noeltaillardat/SmartGasSensor/ltspice/Draft1.asc

C1: cap; 100n
C2: cap; 1µ
C3: cap; 100n
C4: cap; 100n
I1: current; PULSE(50nA 100nA 2s 0.1s 0.1s 2s); AC 1 0
R1: res; 10k
R2: res; 100k
R3: res; 0.5k
R4: res; 100k
R5: res; 1k
U2: LTC1050
V1: voltage; 5
Named nets: 0, vcc, adc, i
;tran 0 6 0 0.01
.ac dec 200 10m 1G
