noeltaillardat/SmartGasSensor/ltspice/Draft2.asc

R1: res
R2: res
R3: res
R4: res
U1: LTC1050
V1: voltage; 2
V2: voltage; 3
V3: voltage; 2
V4: voltage; 5
Named nets: gas_value, offset, diff, warning, 0, vcc
